veroxzik/OpeNITHM/v2-cad/all_layers.jpg

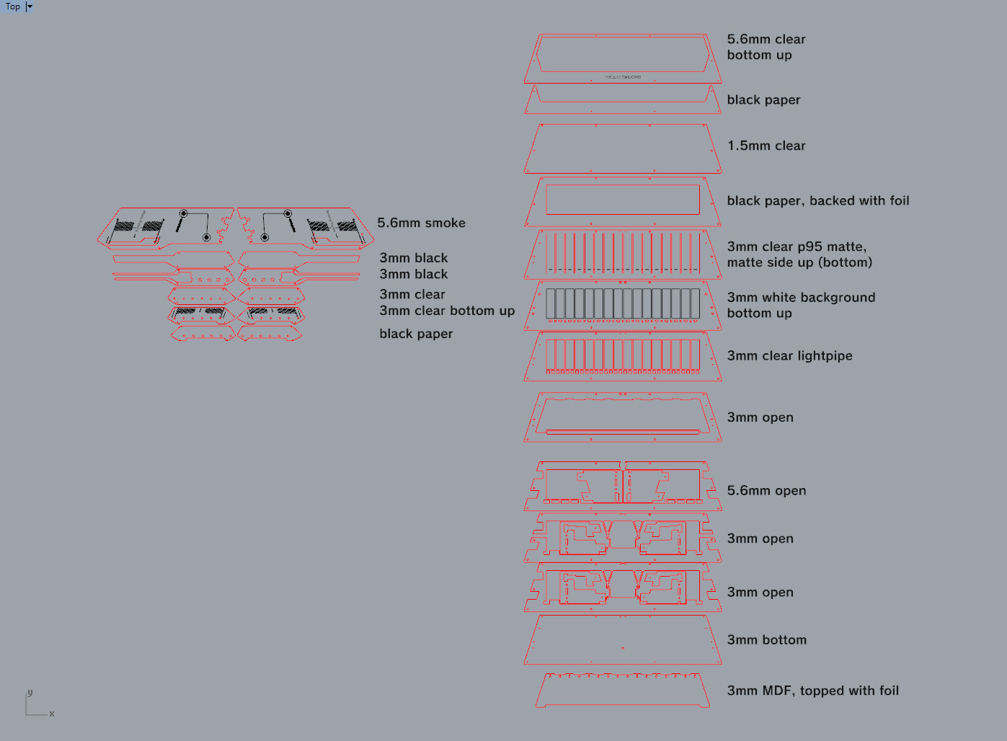
v2-cad/all_layers.jpg
