veroxzik/OpeNITHM/v2-cad/shield_interior_3mm_MDF.dxf

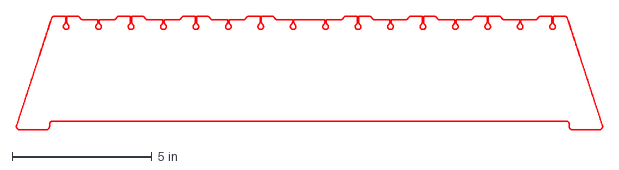
[picture p13: CAD file, 2020-08-10]
v2-cad/shield_interior_3mm_MDF.dxf
21.0 x 4.07 in
