veroxzik/OpeNITHM/v2-cad/top_black_paper.dxf

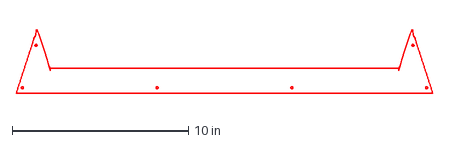
[picture p14: CAD file, 2020-08-10]
v2-cad/top_black_paper.dxf
23.7 x 3.79 in
