veroxzik/OpeNITHM/v2-cad/interior_case_bottom_3mm_black.dxf

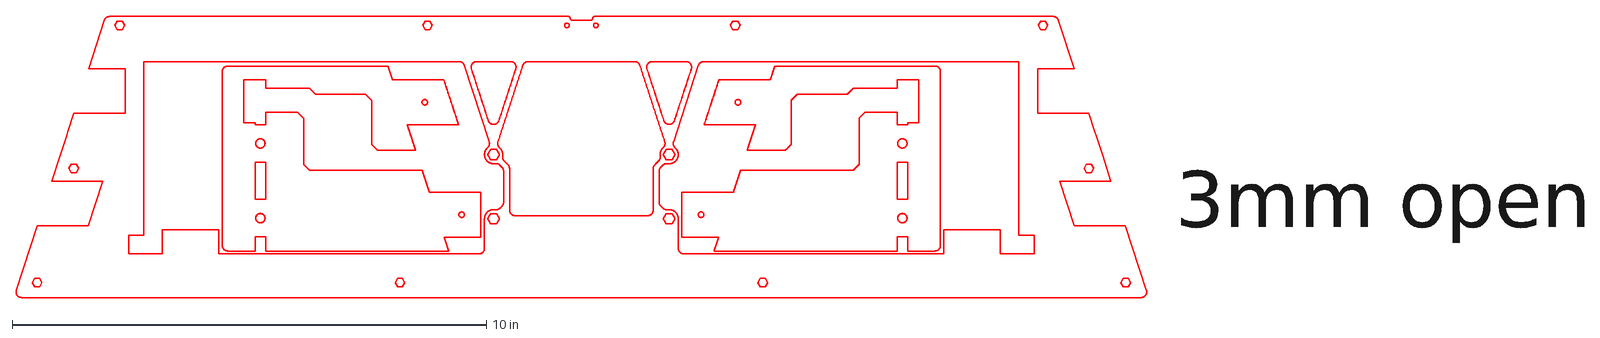
[picture p15: CAD file, 2020-08-10]
v2-cad/interior_case_bottom_3mm_black.dxf
3mm open
