veroxzik/OpeNITHM/v2-cad/interior_case_mid_3mm_black.dxf

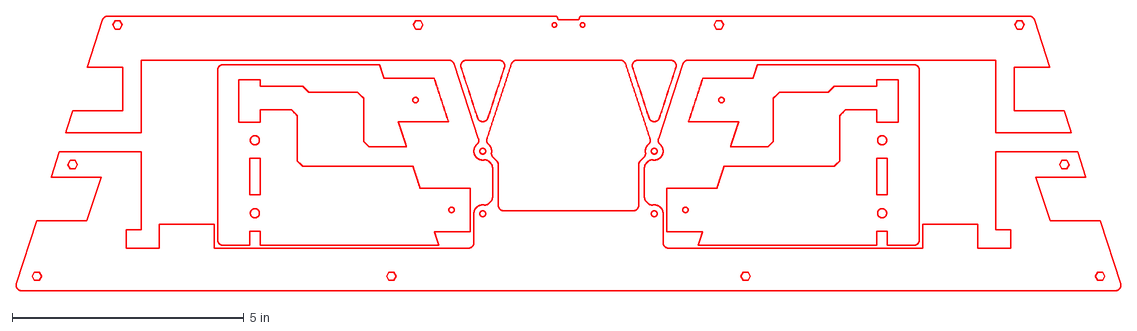
[picture p17: CAD file, 2020-08-10]
v2-cad/interior_case_mid_3mm_black.dxf
23.8 x 5.92 in
