veroxzik/OpeNITHM/v2-cad/thin_surface_layer_1.5mm_clear.dxf

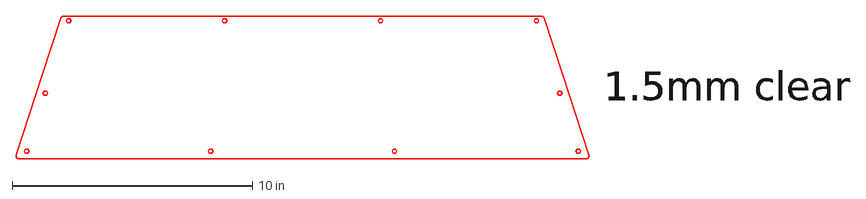
[picture p18: CAD file, 2020-08-10]
v2-cad/thin_surface_layer_1.5mm_clear.dxf
1.5mm clear
