veroxzik/OpeNITHM/v2-cad/bottom_3mm_black.dxf

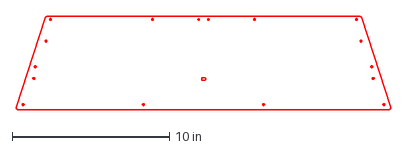
[picture p20: CAD file, 2020-08-10]
v2-cad/bottom_3mm_black.dxf
23.8 x 5.92 in
