veroxzik/OpeNITHM/v2-cad/side_fronts_3mm_clear.dxf

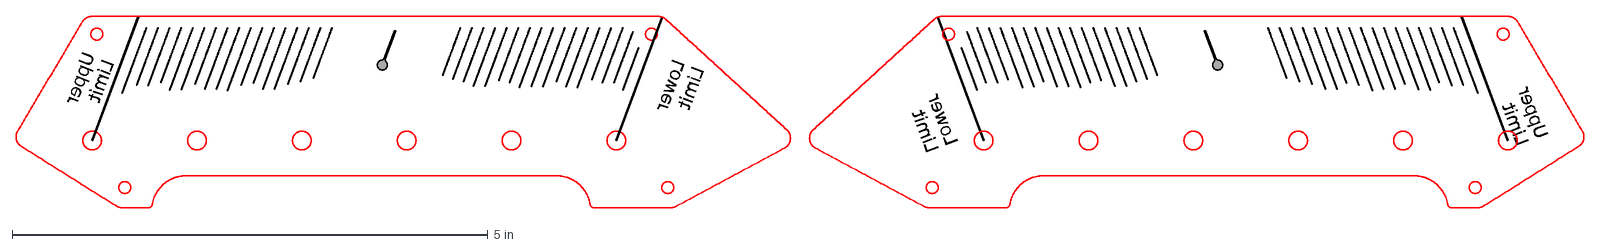
[picture p21: CAD file, 2020-08-10]
v2-cad/side_fronts_3mm_clear.dxf
Upper Limit
Lower Limit
