veroxzik/OpeNITHM/v2-cad/top_layer_5.6mm_clear.dxf

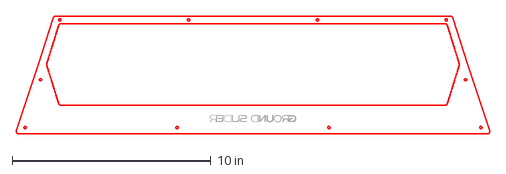
[picture p22: CAD file, 2020-08-10]
v2-cad/top_layer_5.6mm_clear.dxf
23.8 x 5.92 in
