veroxzik/OpeNITHM/v2-cad/side_spacer_3mm_clear.dxf

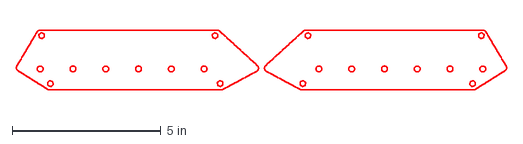
[picture p23: CAD file, 2020-08-10]
v2-cad/side_spacer_3mm_clear.dxf
16.5 x 2.01 in
