veroxzik/OpeNITHM/v2-cad/case-model.obj

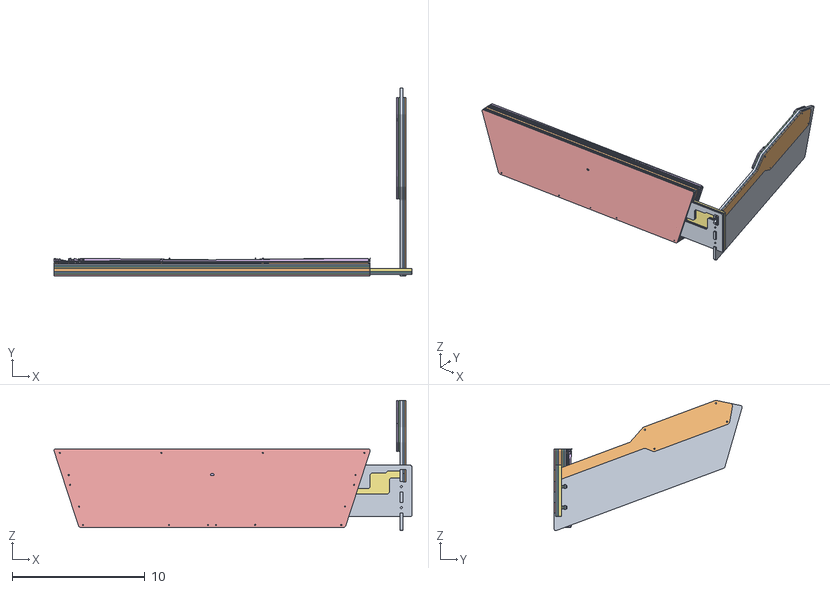
[picture p25: CAD file, 2020-08-10]
v2-cad/case-model.obj
27.0 x 14.2 x 9.81
